jlab-sensing/ENTS-node-hardware/images/annotated/PXL_20250430_212811406.jpg

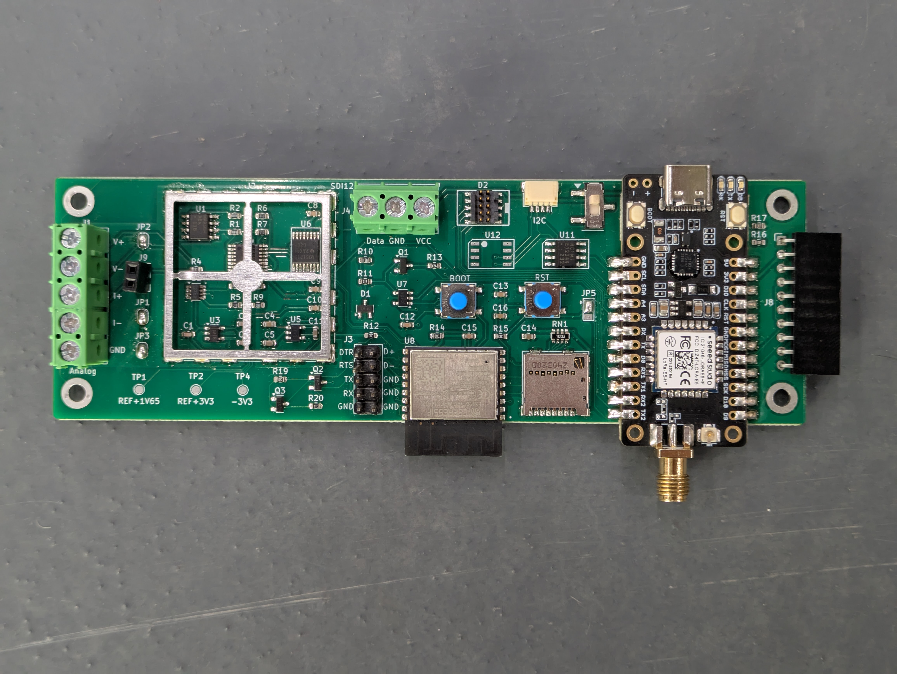
images/annotated/PXL_20250430_212811406.jpg
